mohammadrezasafaeian/usbc-pd-bench-psu/control.kicad_sch

## KiCad design control.kicad_sch (2026-05-25)

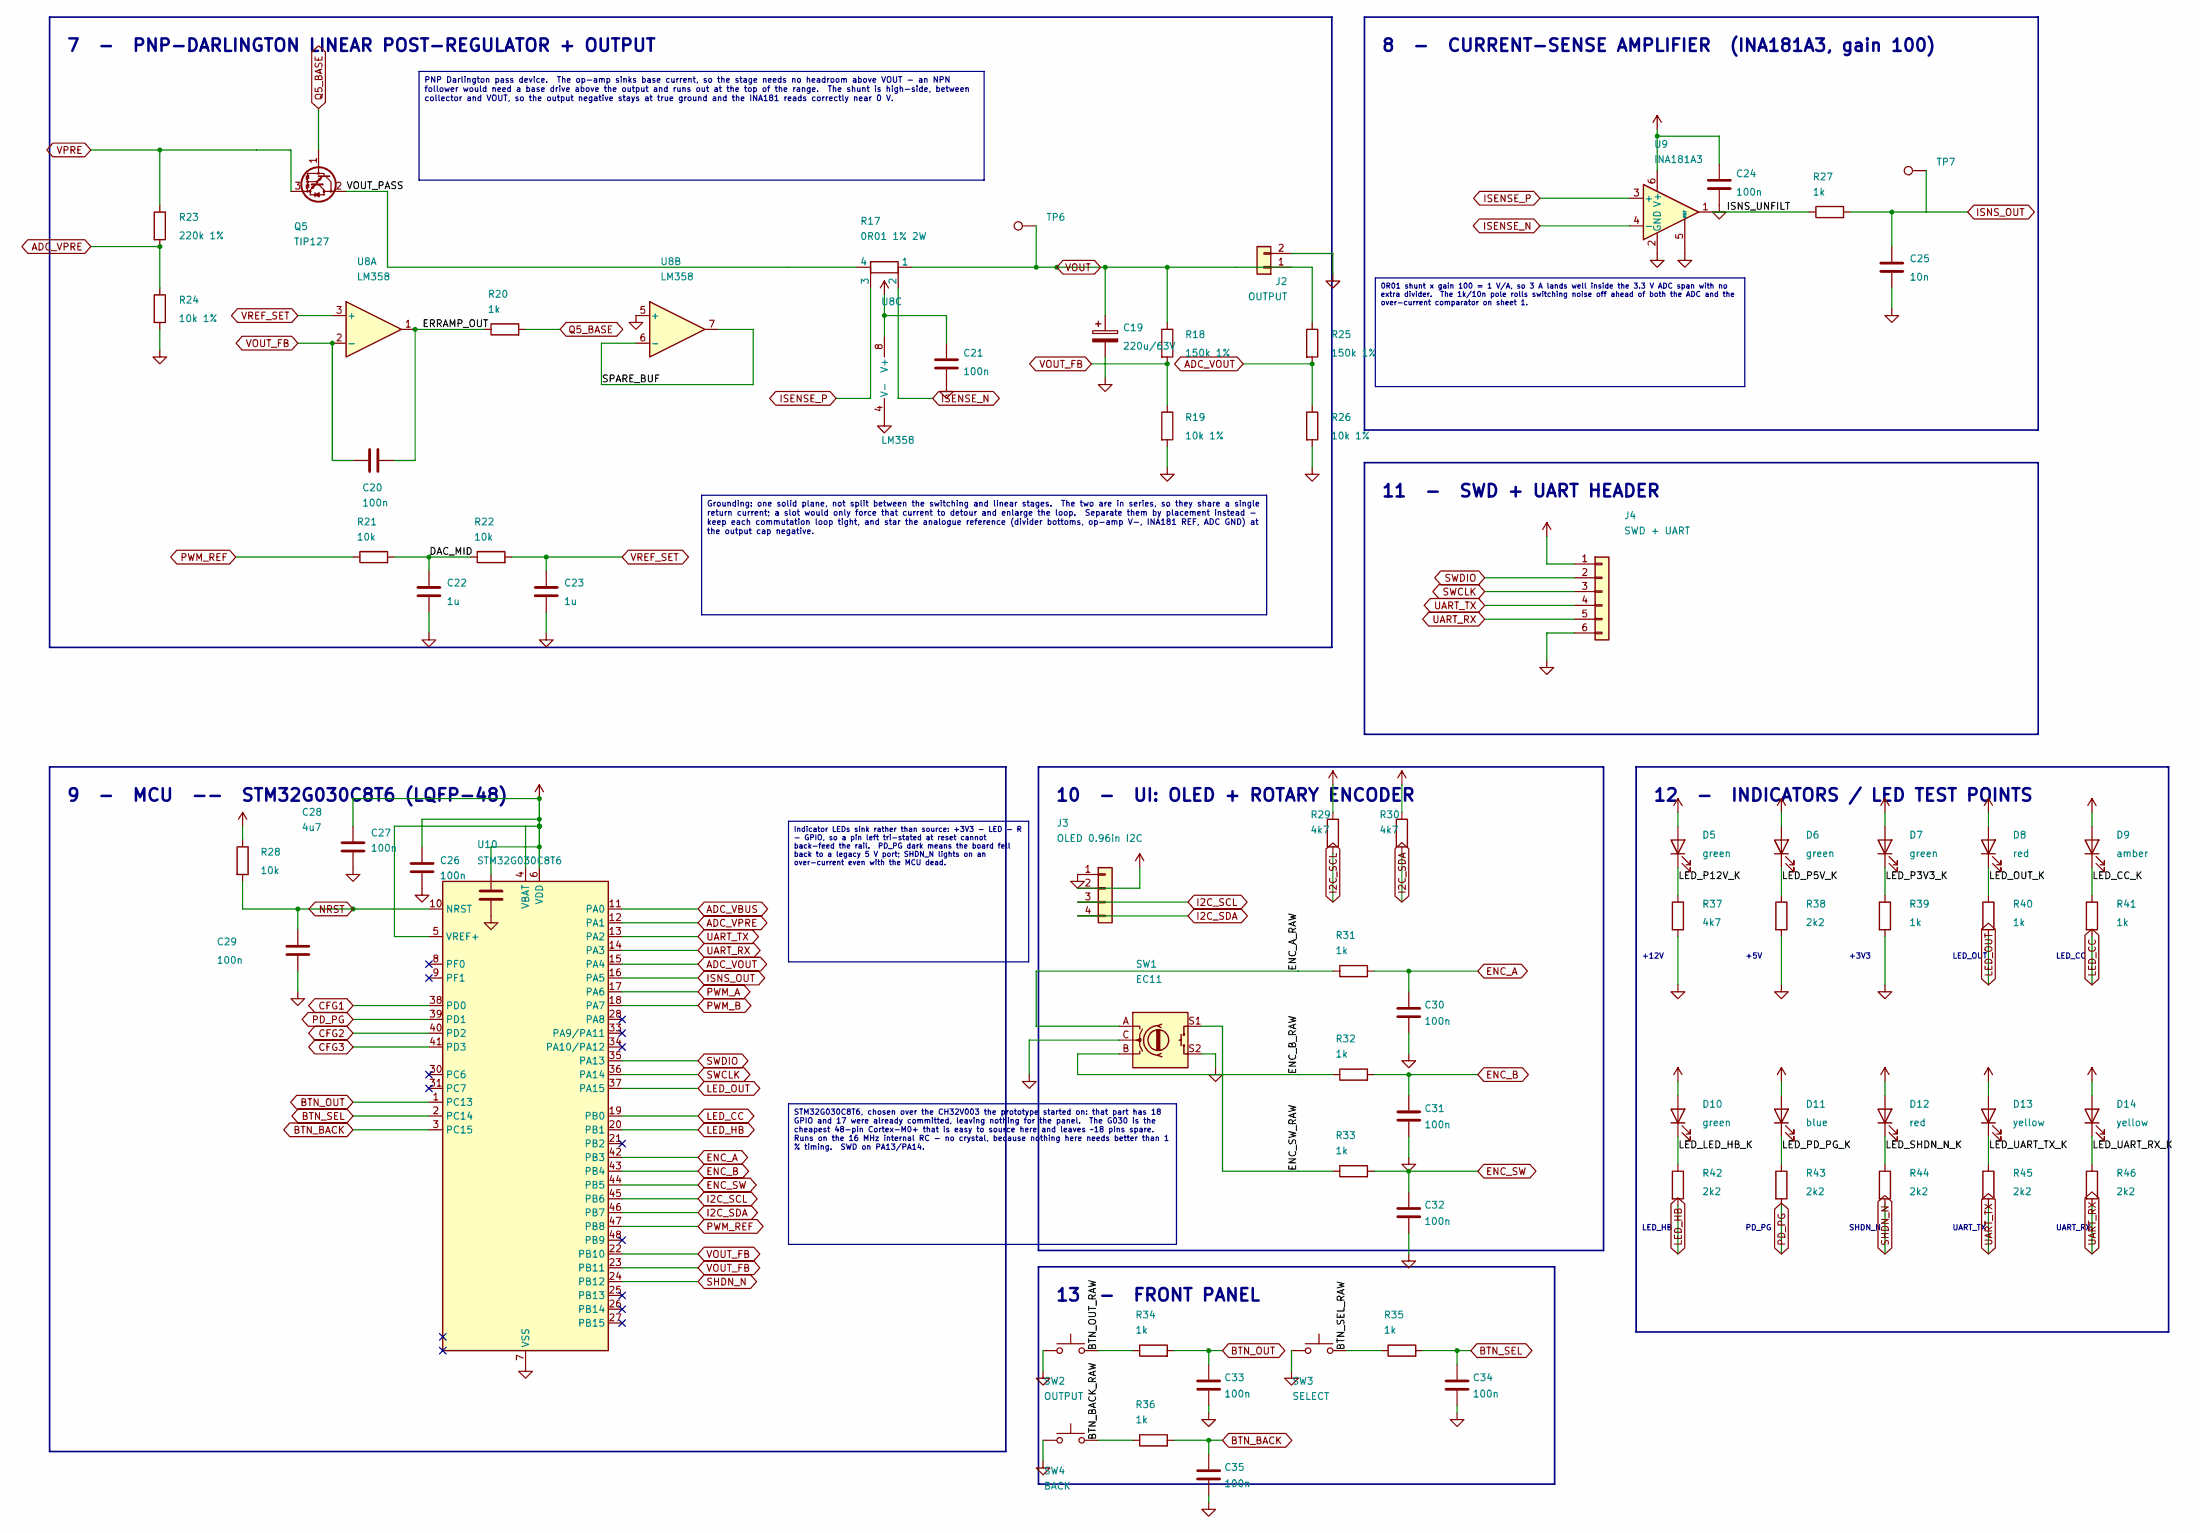
[picture p15: schematic control.kicad_sch]

Parts:
C19: 220u/63V; CP_Elec_6.3x7.7
C20, C21, C24, C26, C27, C29, C30, C31, C32, C33, C34, C35: 100n; C_0805_2012Metric
C22, C23: 1u; C_0805_2012Metric
C25: 10n; C_0805_2012Metric
C28: 4u7; C_0805_2012Metric
D5, D6, D7, D10: green; LED_0805_2012Metric
D8, D12: red; LED_0805_2012Metric
D9: amber; LED_0805_2012Metric
D11: blue; LED_0805_2012Metric
D13, D14: yellow; LED_0805_2012Metric
J2: OUTPUT; PinSocket_1x02_P2.54mm_Vertical
J3: OLED 0.96in I2C; PinHeader_1x04_P2.54mm_Vertical
J4: SWD + UART; PinHeader_1x06_P2.54mm_Vertical
Q5: TIP127; TO-220-3_Vertical
R17: 0R01 1% 2W; R_2512_6332Metric
R18, R25: 150k 1%; R_0805_2012Metric
R19, R24, R26: 10k 1%; R_0805_2012Metric
R20, R27, R31, R32, R33, R34, R35, R36, R39, R40, R41: 1k; R_0805_2012Metric
R21, R22, R28: 10k; R_0805_2012Metric
R23: 220k 1%; R_0805_2012Metric
R29, R30, R37: 4k7; R_0805_2012Metric
R38, R42, R43, R44, R45, R46: 2k2; R_0805_2012Metric
SW1: EC11; RotaryEncoder_Alps_EC11E-Switch_Vertical_H20mm
SW2: OUTPUT; SW_SPST_B3S-1000
SW3: SELECT; SW_SPST_B3S-1000
SW4: BACK; SW_SPST_B3S-1000
TP6: TP_VOUT; TestPoint_Pad_D1.5mm
TP7: TP_ISNS; TestPoint_Pad_D1.5mm
U8: LM358; SOIC-8_3.9x4.9mm_P1.27mm
U9: INA181A3; SOT-23-5
U10: STM32G030C8T6; LQFP-48_7x7mm_P0.5mm

Connections:
+3V3: C26.1, C27.1, C28.1, D7.2 (A), D8.2 (A), D9.2 (A), D10.2 (A), D11.2 (A), D12.2 (A), D13.2 (A), D14.2 (A), J3.2, J4.1, R28.1, R29.1, R30.1, U10.4 (VBAT), U10.5 (VREF+), U10.6 (VDD)
+5V: C24.1, D6.2 (A), U9.6 (V+)
+12V: C21.1, D5.2 (A), U8.8 (V+)
ADC_VBUS: U10.11 (PA0)
ADC_VOUT: R25.2, R26.1, U10.15 (PA4)
ADC_VPRE: R23.2, R24.1, U10.12 (PA1)
BTN_BACK: C35.1, R36.2, U10.3 (PC15)
BTN_BACK_RAW: R36.1, SW4.2
BTN_OUT: C33.1, R34.2, U10.1 (PC13)
BTN_OUT_RAW: R34.1, SW2.2
BTN_SEL: C34.1, R35.2, U10.2 (PC14)
BTN_SEL_RAW: R35.1, SW3.2
CFG1: U10.38 (PD0)
CFG2: U10.40 (PD2)
CFG3: U10.41 (PD3)
DAC_MID: C22.1, R21.2, R22.1
ENC_A: C30.1, R31.2, U10.42 (PB3)
ENC_A_RAW: R31.1, SW1.A
ENC_B: C31.1, R32.2, U10.43 (PB4)
ENC_B_RAW: R32.1, SW1.B
ENC_SW: C32.1, R33.2, U10.44 (PB5)
ENC_SW_RAW: R33.1, SW1.S1
ERRAMP_OUT: C20.2, R20.1, U8.1
GND: C19.2, C21.2, C22.2, C23.2, C24.2, C25.2, C26.2, C27.2, C28.2, C29.2, C30.2, C31.2, C32.2, C33.2, C34.2, C35.2, J2.2, J3.1, J4.6, R19.2, R24.2, R26.2, R37.2, R38.2, R39.2, SW1.C, SW1.S2, SW2.1, SW3.1, SW4.1, U8.4 (V-), U8.5 (+), U9.2 (GND), U9.5 (REF), U10.7 (VSS)
I2C_SCL: J3.3, R29.2, U10.45 (PB6)
I2C_SDA: J3.4, R30.2, U10.46 (PB7)
ISENSE_N: R17.2, U9.4 (-)
ISENSE_P: R17.3, U9.3 (+)
ISNS_OUT: C25.1, R27.2, TP7.1, U10.16 (PA5)
ISNS_UNFILT: R27.1, U9.1
LED_CC: R41.2, U10.19 (PB0)
LED_CC_K: D9.1 (K), R41.1
LED_HB: R42.2, U10.20 (PB1)
LED_LED_HB_K: D10.1 (K), R42.1
LED_OUT: R40.2, U10.37 (PA15)
LED_OUT_K: D8.1 (K), R40.1
LED_P3V3_K: D7.1 (K), R39.1
LED_P5V_K: D6.1 (K), R38.1
LED_P12V_K: D5.1 (K), R37.1
LED_PD_PG_K: D11.1 (K), R43.1
LED_SHDN_N_K: D12.1 (K), R44.1
LED_UART_RX_K: D14.1 (K), R46.1
LED_UART_TX_K: D13.1 (K), R45.1
NRST: C29.1, R28.2, U10.10 (NRST)
PD_PG: R43.2, U10.39 (PD1)
PWM_A: U10.17 (PA6)
PWM_B: U10.18 (PA7)
PWM_REF: R21.1, U10.47 (PB8)
Q5_BASE: Q5.1 (B), R20.2
SHDN_N: R44.2, U10.24 (PB12)
SPARE_BUF: U8.6 (-), U8.7
SWCLK: J4.3, U10.36 (PA14)
SWDIO: J4.2, U10.35 (PA13)
UART_RX: J4.5, R46.2, U10.14 (PA3)
UART_TX: J4.4, R45.2, U10.13 (PA2)
VOUT: C19.1, J2.1, R17.1, R18.1, R25.1, TP6.1
VOUT_FB: C20.1, R18.2, R19.1, U8.2 (-), U10.22 (PB10), U10.23 (PB11)
VOUT_PASS: Q5.2 (C), R17.4
VPRE: Q5.3 (E), R23.1
VREF_SET: C23.1, R22.2, U8.3 (+)

Notes on the sheet:
+12V
+5V
+3V3
LED_OUT
LED_CC
LED_HB
PD_PG
SHDN_N
UART_TX
UART_RX
7 - PNP-DARLINGTON LINEAR POST-REGULATOR + OUTPUT
8 - CURRENT-SENSE AMPLIFIER (INA181A3, gain 100)
9 - MCU -- STM32G030C8T6 (LQFP-48)
10 - UI: OLED + ROTARY ENCODER
13 - FRONT PANEL
12 - INDICATORS / LED TEST POINTS
11 - SWD + UART HEADER
0R01 shunt x gain 100 = 1 V/A, so 3 A lands well inside the 3.3 V ADC span with no extra divider. The 1k/10n pole rolls switching noise off ahead of both the ADC and the over-current comparator on sheet 1.
PNP Darlington pass device. The op-amp sinks base current, so the stage needs no headroom above VOUT - an NPN follower would need a base drive above the output and runs out at the top of the range. The shunt is high-side, between collector and VOUT, so the output negative stays at true ground and t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
Grounding: one solid plane, not split between the switching and linear stages. The two are in series, so they share a single return current; a slot would only force that current to detour and enlarge the loop. Separate them by placement instead - keep each commutation loop tight, and star the analo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
STM32G030C8T6, chosen over the CH32V003 the prototype started on: that part has 18 GPIO and 17 were already committed, leaving nothing for the panel. The G030 is the cheapest 48-pin Cortex-M0+ that is easy to source here and leaves ~18 pins spare. Runs on the 16 MHz internal RC - no crystal, becaus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
Indicator LEDs sink rather than source: +3V3 - LED - R - GPIO, so a pin left tri-stated at reset cannot back-feed the rail. PD_PG dark means the board fell back to a legacy 5 V port; SHDN_N lights on an over-current even with the MCU dead.
