mohammadrezasafaeian/usbc-pd-bench-psu/power.kicad_sch

## KiCad design power.kicad_sch (2026-05-25)

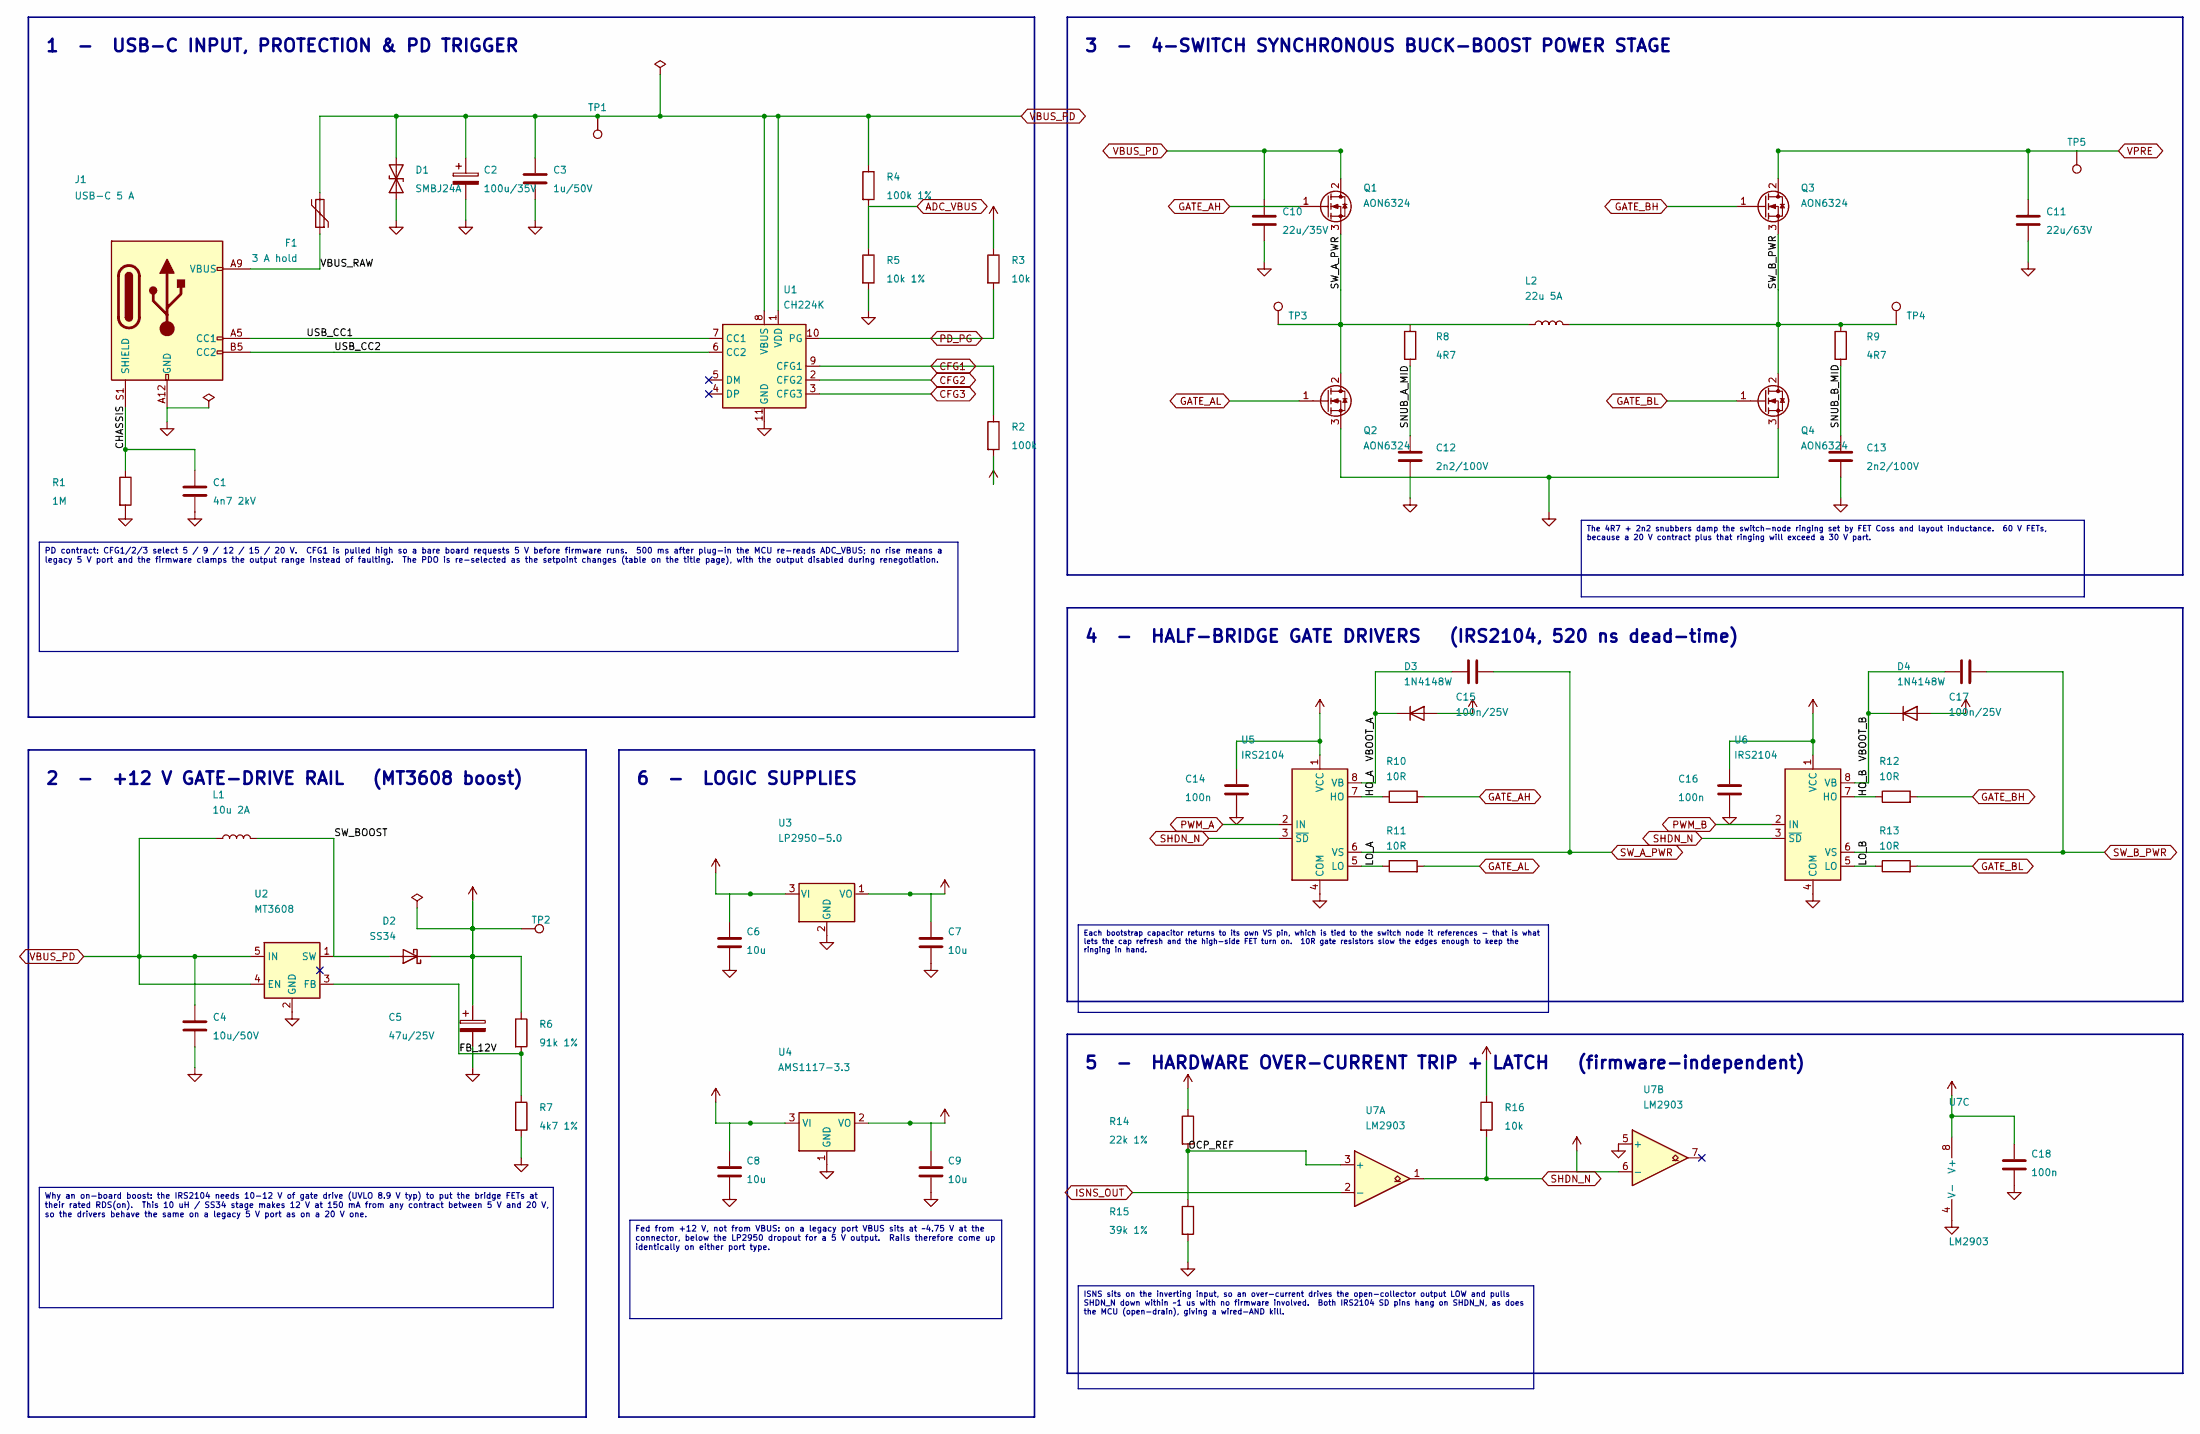
[picture p16: schematic power.kicad_sch]

Parts:
C1: 4n7 2kV; C_0805_2012Metric
C2: 100u/35V; CP_Elec_6.3x7.7
C3: 1u/50V; C_0805_2012Metric
C4: 10u/50V; C_0805_2012Metric
C5: 47u/25V; CP_Elec_6.3x7.7
C6, C7, C8, C9: 10u; C_0805_2012Metric
C10: 22u/35V; C_0805_2012Metric
C11: 22u/63V; C_0805_2012Metric
C12, C13: 2n2/100V; C_0805_2012Metric
C14, C16, C18: 100n; C_0805_2012Metric
C15, C17: 100n/25V; C_0805_2012Metric
D1: SMBJ24A; D_SMA
D2: SS34; D_SMA
D3, D4: 1N4148W; D_SOD-123
F1: 3 A hold; Fuse_1206_3216Metric
J1: USB-C 5 A; USB_C_Receptacle_XKB_U262-16XN-4BVC11
L1: 10u 2A; L_12x12mm_H8mm
L2: 22u 5A; L_12x12mm_H8mm
Q1, Q2, Q3, Q4: AON6324; TO-263-2
R1: 1M; R_0805_2012Metric
R2: 100k; R_0805_2012Metric
R3, R16: 10k; R_0805_2012Metric
R4: 100k 1%; R_0805_2012Metric
R5: 10k 1%; R_0805_2012Metric
R6: 91k 1%; R_0805_2012Metric
R7: 4k7 1%; R_0805_2012Metric
R8, R9: 4R7; R_0805_2012Metric
R10, R11, R12, R13: 10R; R_0805_2012Metric
R14: 22k 1%; R_0805_2012Metric
R15: 39k 1%; R_0805_2012Metric
TP1: TP_VBUS; TestPoint_Pad_D1.5mm
TP2: TP_12V; TestPoint_Pad_D1.5mm
TP3: TP_SWA; TestPoint_Pad_D1.0mm
TP4: TP_SWB; TestPoint_Pad_D1.0mm
TP5: TP_VPRE; TestPoint_Pad_D1.5mm
U1: CH224K; SSOP-10-1EP_3.9x4.9mm_P1mm_EP2.1x3.3mm
U2: MT3608; SOT-23-5
U3: LP2950-5.0; SOT-223-3_TabPin2
U4: AMS1117-3.3; SOT-223-3_TabPin2
U5, U6: IRS2104; SOIC-8_3.9x4.9mm_P1.27mm
U7: LM2903; SOIC-8_3.9x4.9mm_P1.27mm

Connections:
+3V3: C9.1, R2.2, R3.1, U4.2 (VO)
+5V: C7.1, C8.1, C18.1, R14.1, R16.1, U3.1 (VO), U4.3 (VI), U7.6 (-), U7.8 (V+)
+12V: C1.2, C2.1, C2.2, C3.1, C3.2, C4.1, C4.2, C5.1, C5.2, C6.1, C6.2, C7.2, C8.2, C9.2, C10.1, C10.2, C11.2, C12.2, C13.2, C14.1, C14.2, C16.1, C16.2, C18.2, D1.1 (A1), D1.2 (A2), D2.1 (K), D3.2 (A), D4.2 (A), F1.2, J1.A12 (GND), J1.B12 (GND), L1.1, Q1.2 (D), Q2.3 (S), Q4.3 (S), R1.2, R4.1, R5.2, R6.1, R7.2, R15.2, TP1.1, TP2.1, U1.1 (VDD), U1.8 (VBUS), U1.11 (GND), U2.2 (GND), U2.4 (EN), U2.5 (IN), U3.2 (GND), U3.3 (VI), U4.1 (GND), U5.1 (VCC), U5.4 (COM), U6.1 (VCC), U6.4 (COM), U7.4 (V-), U7.5 (+)
ADC_VBUS: R4.2, R5.1
CFG1: R2.1, U1.9 (CFG1)
CFG2: U1.2 (CFG2)
CFG3: U1.3 (CFG3)
CHASSIS: C1.1, J1.S1 (SHIELD), R1.1
FB_12V: R6.2, R7.1, U2.3 (FB)
GATE_AH: Q1.1 (G), R10.2
GATE_AL: Q2.1 (G), R11.2
GATE_BH: Q3.1 (G), R12.2
GATE_BL: Q4.1 (G), R13.2
HO_A: R10.1, U5.7 (HO)
HO_B: R12.1, U6.7 (HO)
ISNS_OUT: U7.2 (-)
LO_A: R11.1, U5.5 (LO)
LO_B: R13.1, U6.5 (LO)
OCP_REF: R14.2, R15.1, U7.3 (+)
PD_PG: R3.2, U1.10 (PG)
PWM_A: U5.2 (IN)
PWM_B: U6.2 (IN)
SHDN_N: R16.2, U5.3 (~SD), U6.3 (~SD), U7.1
SNUB_A_MID: C12.1, R8.2
SNUB_B_MID: C13.1, R9.2
SW_A_PWR: C15.2, L2.1, Q1.3 (S), Q2.2 (D), R8.1, TP3.1, U5.6 (VS)
SW_BOOST: D2.2 (A), L1.2, U2.1 (SW)
SW_B_PWR: C17.2, L2.2, Q3.3 (S), Q4.2 (D), R9.1, TP4.1, U6.6 (VS)
USB_CC1: J1.A5 (CC1), U1.7 (CC1)
USB_CC2: J1.B5 (CC2), U1.6 (CC2)
VBOOT_A: C15.1, D3.1 (K), U5.8 (VB)
VBOOT_B: C17.1, D4.1 (K), U6.8 (VB)
VBUS_RAW: F1.1, J1.A9 (VBUS), J1.B9 (VBUS)
VPRE: C11.1, Q3.2 (D), TP5.1

Notes on the sheet:
1 - USB-C INPUT, PROTECTION & PD TRIGGER
2 - +12 V GATE-DRIVE RAIL (MT3608 boost)
6 - LOGIC SUPPLIES
3 - 4-SWITCH SYNCHRONOUS BUCK-BOOST POWER STAGE
4 - HALF-BRIDGE GATE DRIVERS (IRS2104, 520 ns dead-time)
5 - HARDWARE OVER-CURRENT TRIP + LATCH (firmware-independent)
Fed from +12 V, not from VBUS: on a legacy port VBUS sits at ~4.75 V at the connector, below the LP2950 dropout for a 5 V output. Rails therefore come up identically on either port type.
Why an on-board boost: the IRS2104 needs 10-12 V of gate drive (UVLO 8.9 V typ) to put the bridge FETs at their rated RDS(on). This 10 uH / SS34 stage makes 12 V at 150 mA from any contract between 5 V and 20 V, so the drivers behave the same on a legacy 5 V port as on a 20 V one.
ISNS sits on the inverting input, so an over-current drives the open-collector output LOW and pulls SHDN_N down within ~1 us with no firmware involved. Both IRS2104 SD pins hang on SHDN_N, as does the MCU (open-drain), giving a wired-AND kill.
The 4R7 + 2n2 snubbers damp the switch-node ringing set by FET Coss and layout inductance. 60 V FETs, because a 20 V contract plus that ringing will exceed a 30 V part.
PD contract: CFG1/2/3 select 5 / 9 / 12 / 15 / 20 V. CFG1 is pulled high so a bare board requests 5 V before firmware runs. 500 ms after plug-in the MCU re-reads ADC_VBUS; no rise means a legacy 5 V port and the firmware clamps the output range instead of faulting. The PDO is re-selected as the set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
Each bootstrap capacitor returns to its own VS pin, which is tied to the switch node it references - that is what lets the cap refresh and the high-side FET turn on. 10R gate resistors slow the edges enough to keep the ringing in hand.
